Community-Sensor-Lab/Air-Quality-Sensor/Content/10. AQS-PCB-Mount.md

**Finding Files \-** File for both the PCB and Senserion Mount will be located on the [Community Sensor Github](https://github.com/Community-Sensor-Lab/Air-Quality-Sensor/tree/master) 

- Download and import the STL files into your 3D Printing Software  
- Add supports wherever required

****

---

**Mounting**

- When the two mounts are completed thread the holes with a 6-32 thread (Not required on newest mount iterations)  

- Secure the AQS Mount onto the top hole with a Grainger \#6 Screw (6-32 x 12'' Phillip Head Screw) with a 6-32 lock nut and a Phillips Bit or 6-32 x 12” Screw with a 6-32 lock nut and a H2.5 Bit. (Make sure that the PCB is screwed into the side with the Lip. So that the PCB will be secure in a vertical position)  
    
- Insert the Sen5X into the Mount  

- Make sure that the holes line up for the SEX5X Mount and the PCB Board  
    
- Secure the SEN5X Mount using the hole in the middle of the PCB. 6-32 x 12” Screw with a 6-32 lock nut and a H2.5 Bit or 6-32 x 12'' Phillip Head Screw (This mount should be on the back of the PCB with all the soldered joints)  

- Insert the AQS into a 3in PVC Pipe. (It is a tight fit so try to use moderate pressure. While rotating the AQS for it to be fully placed into the PVC Pipe.)

[image1]: <>

[image2]: <>

[image3]: <>
