Community-Sensor-Lab/Air-Quality-Sensor/Content/5. Code-Activity.md

Code Activity  
	In this section we're going to get an understanding on where the main code comes from by merging example codes. When merging example codes, we’ll be able to test and run two sensors at once. For this exercise we’ll be using the SparkFun single shot code and the BME280 test code.   
	If you don’t already have the library installed; be sure to install SparkFun SCD4x Arduino Library through the library manager. As this is where you will be able to find the single shot example code. 

Opening Up Both Example Codes  
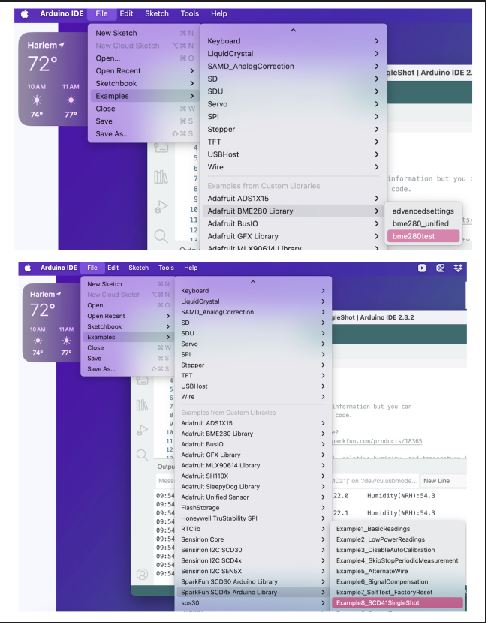
[picture p43: images/Code_Activity1.JPG]
  
SCD41SingleShot Edit  
	  
Before we continue we will have to make a slight modification to the code. Highlight lines 76 through 92 and click command forward slash (mac) or control forward slash (windows). This will comment out that section of the code, so that the section is disabled when uploading it. Also change line 35 to false,false,false. 

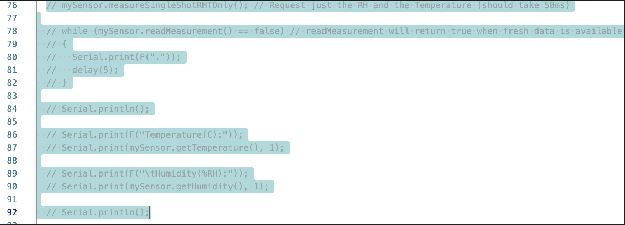
[picture p44: images/Code_Activity2.JPG]


Now we have everything read to start merging the code.

Procedure

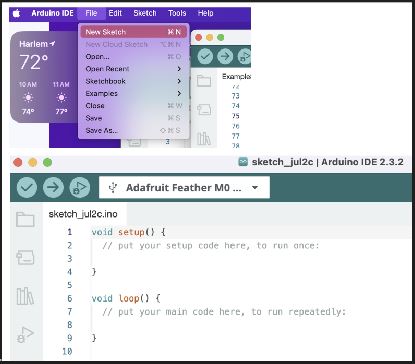
[picture p45: images/Code_Activity3.JPG]
1. Let’s start off by creating and setting up our new sketch.  
2. In the sketch we will start off by creating tabs for our functions  
   1. We will have four tabs:  
      1. SCD41\_initial   
      2. BME280\_initial  
      3. SCD41\_loop  
      4. BME280\_loop  
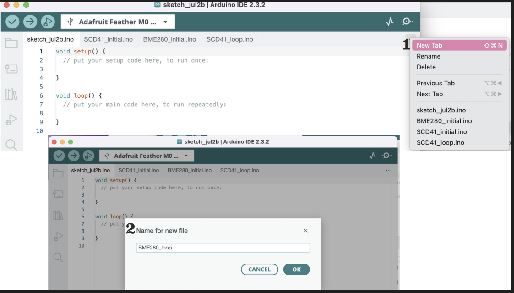
[picture p46: images/Code_Activity4.JPG]
   2. Creating these functions will help us better manage our code.  
3. Start by copying over the section before void setup() from both example codes and pasting it on to our new sketch before void setup().  

4. Next copy over the code for each tab we have created.  
     
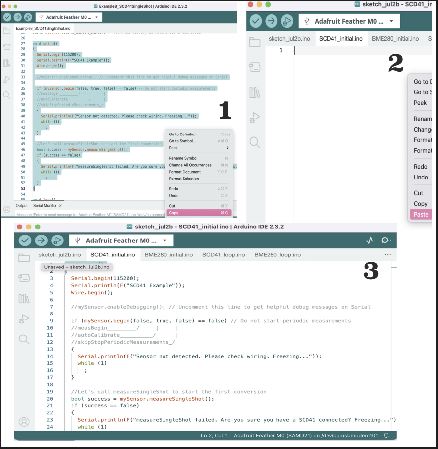
[picture p47: images/Code_Activity5.JPG]
   1. For the SCD 41\_initial we will copy over the void setup() code    
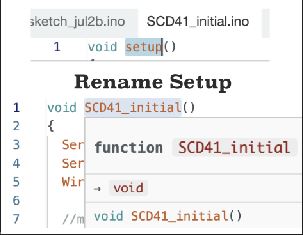
[picture p48: images/Code_Activity6.JPG]
      1. Next we will give the function a new name by replacing setup() with SCD41\_initial (recommended) or choose your own name.  
      2. Choose a good name as it will stick and you want to be able to easily identify the function  
   2. Repeat the same steps for the BME280\_initial tab.  
      1. Copy the void setup code  
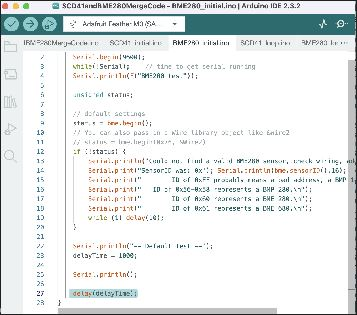
[picture p49: images/Code_Activity7.JPG]
      2. Paste it into the tab   
         1. Add “ delay(delayTime); ” into the end of the function as shown above   
      3. Remove printValues() in line 70 under void loop(););  
         1. Copy and Paste lines 76 to line 93 into Void loop. This function should be put under the tab BME280\_loop.  
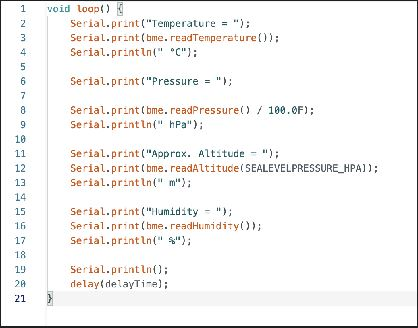
[picture p50: images/Code_Activity8.JPG]
            

      4. Rename the function  
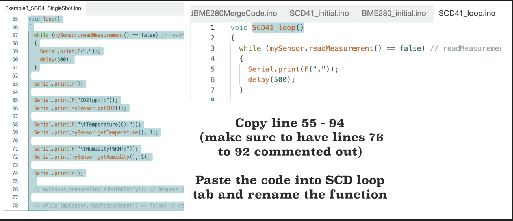
[picture p51: images/Code_Activity9.JPG]
   3. For the SCD 41 loop we will be copying the over the void loop code into the tab and renaming the function as well.  
   4. Repeat the same process for copying over the BME 280 loop into the BME280\_loop tab.  
      1. Copy over the void printValues  
      2. And add delay(delayTime); under the Serial.println();

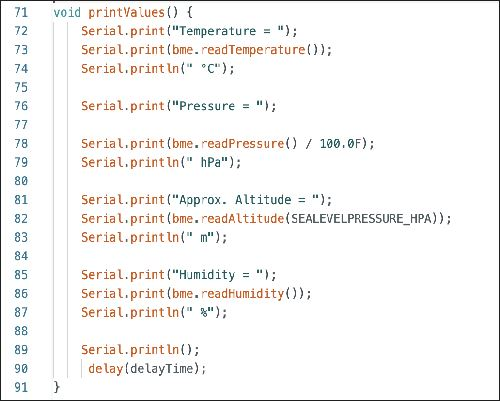
[picture p52: images/Code_Activity10.JPG]


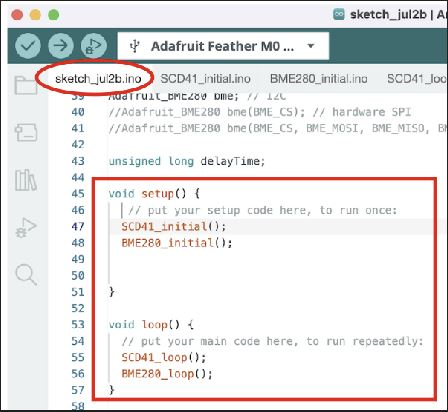
[picture p53: images/Code_Activity11.JPG]
5. Now we will add the functions we have created to the first tab like so;   
6. Our code is now complete\!  
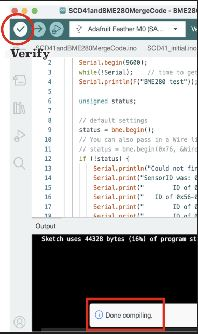
[picture p54: images/Code_Activity12.JPG]
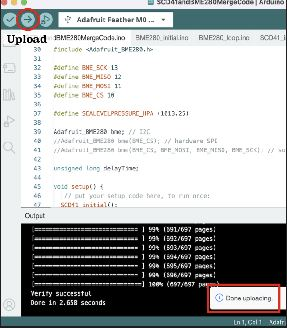
[picture p55: images/Code_Activity13.JPG]
7. Next step is to verify and upload the code to our sensors    
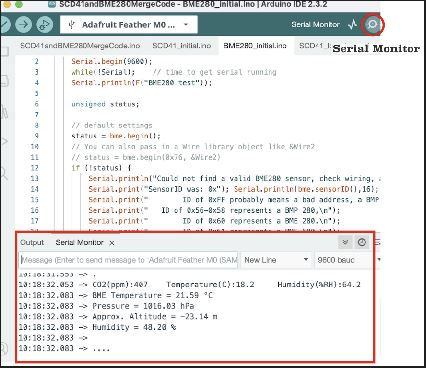
[picture p56: images/Code_Activity14.JPG]
8. Once the upload is complete press the serial monitor at the top right corner to see your data results.

[image1]: <>

[image2]: <>

[image3]: <>

[image4]: <>

[image5]: <>

[image6]: <>

[image7]: <>

[image8]: <>

[image9]: <>

[image10]: <>

[image11]: <>

[image12]: <>

[image13]: <>

[image14]: <>
