Community-Sensor-Lab/Air-Quality-Sensor/Content/image-1.png

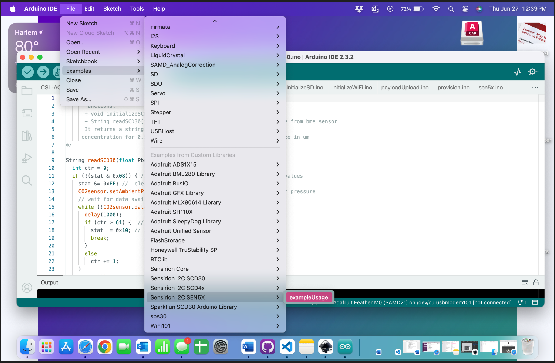
Content/image-1.png
