Community-Sensor-Lab/Air-Quality-Sensor/Content/image.png

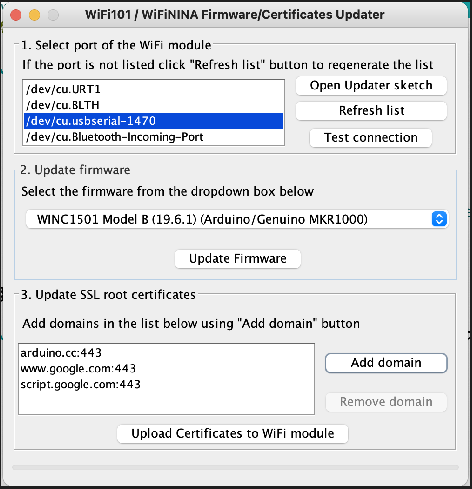
Content/image.png
