Community-Sensor-Lab/Air-Quality-Sensor/Contents/air_mon_system_sqr1.png

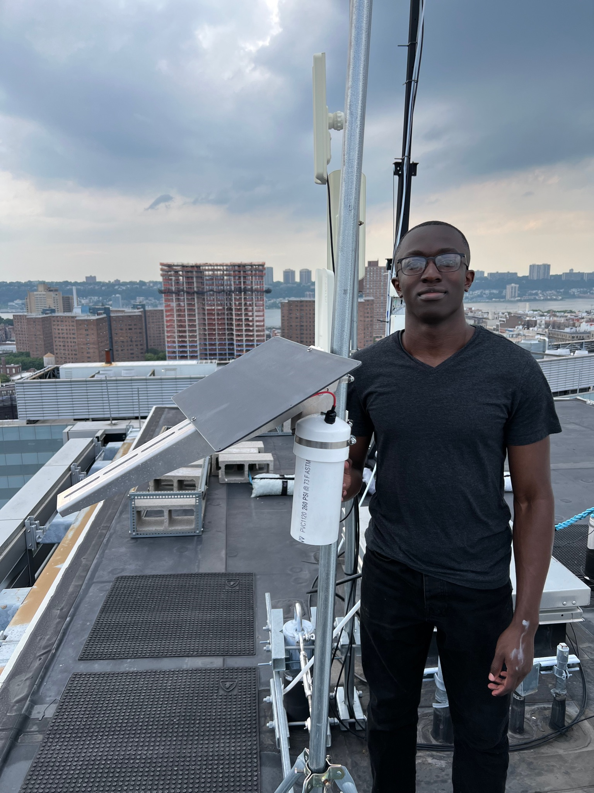
Contents/air_mon_system_sqr1.png
