Community-Sensor-Lab/Air-Quality-Sensor/Contents/CSL_AQS_solar_sqr.png

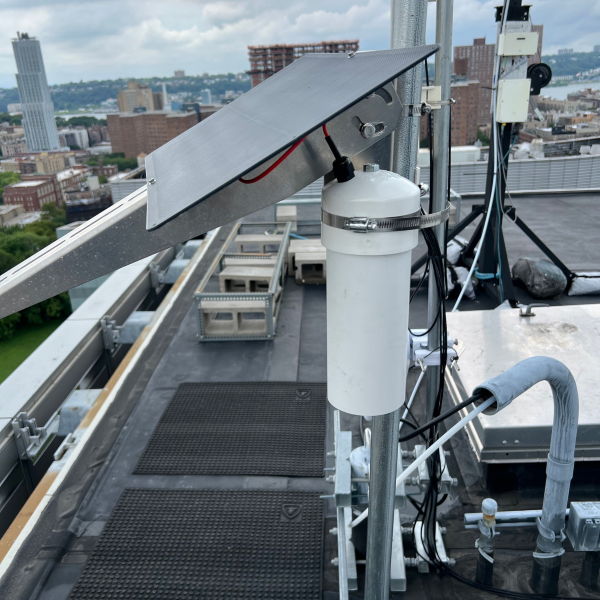
Contents/CSL_AQS_solar_sqr.png
