Community-Sensor-Lab/Air-Quality-Sensor/Contents/image-52.png

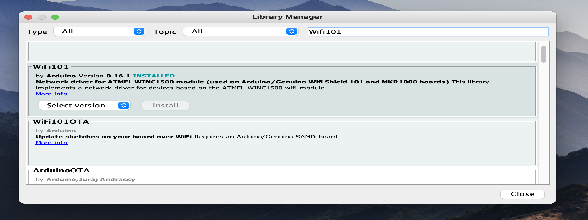
Contents/image-52.png
