Community-Sensor-Lab/Air-Quality-Sensor/Contents/image-53.png

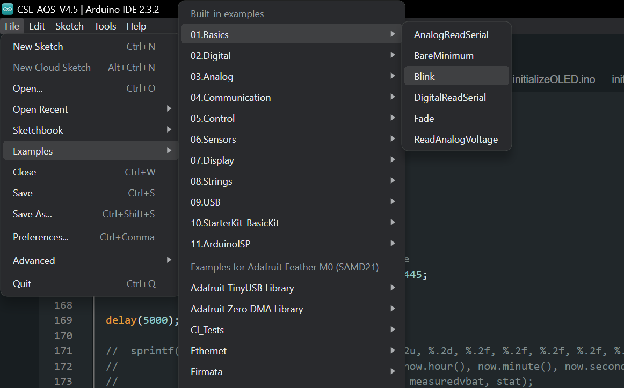
Contents/image-53.png
