Community-Sensor-Lab/Air-Quality-Sensor/Contents/image-54.png

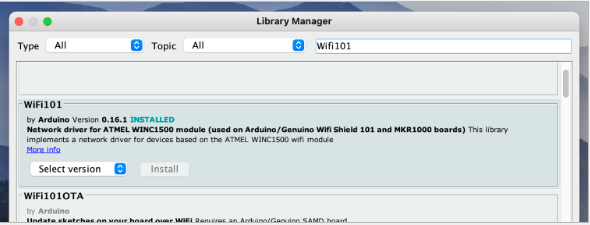
Contents/image-54.png
