Community-Sensor-Lab/Air-Quality-Sensor/Contents/image-55.png

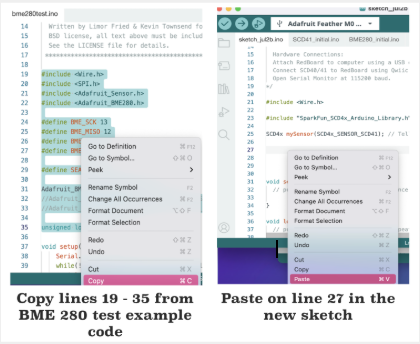
Contents/image-55.png
