Community-Sensor-Lab/Air-Quality-Sensor/Contents/resized_images/image-21.png

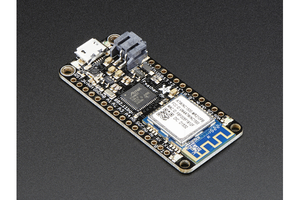
Contents/resized_images/image-21.png
