Community-Sensor-Lab/Air-Quality-Sensor/Contents/resized_images/image-22.png

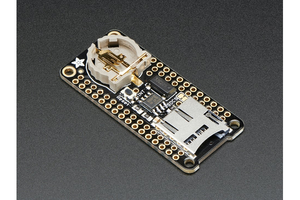
Contents/resized_images/image-22.png
