Community-Sensor-Lab/Air-Quality-Sensor/Contents/resized_images/image-23.png

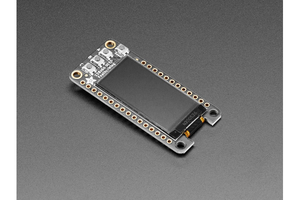
Contents/resized_images/image-23.png
