Community-Sensor-Lab/Air-Quality-Sensor/Contents/resized_images/image-24.png

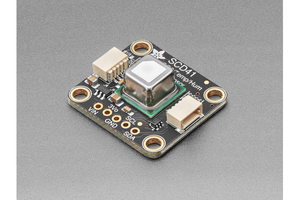
Contents/resized_images/image-24.png
