Community-Sensor-Lab/Air-Quality-Sensor/Contents/resized_images/image-25.png

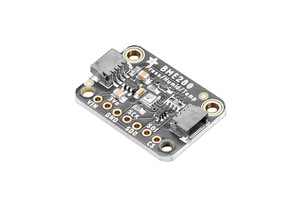
Contents/resized_images/image-25.png
