Community-Sensor-Lab/Air-Quality-Sensor/Contents/resized_images/image-26.png

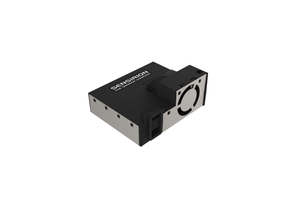
Contents/resized_images/image-26.png
