Community-Sensor-Lab/Air-Quality-Sensor/Contents/resized_images/image-27.png

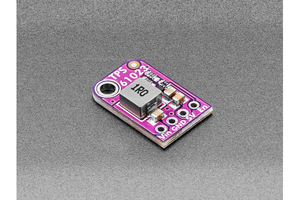
Contents/resized_images/image-27.png
