Community-Sensor-Lab/Air-Quality-Sensor/Contents/resized_images/image-28.png

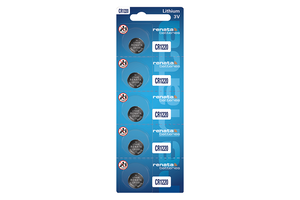
Contents/resized_images/image-28.png
