Community-Sensor-Lab/Air-Quality-Sensor/Contents/resized_images/image-29.png

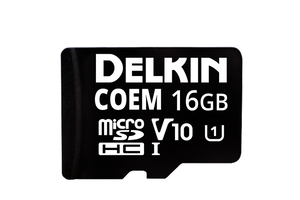
Contents/resized_images/image-29.png
