Community-Sensor-Lab/Air-Quality-Sensor/Contents/resized_images/image-30.png

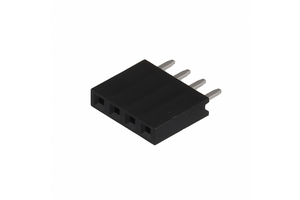
Contents/resized_images/image-30.png
