Community-Sensor-Lab/Air-Quality-Sensor/Contents/resized_images/image-31.png

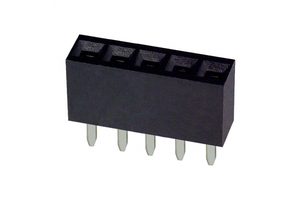
Contents/resized_images/image-31.png
