Community-Sensor-Lab/Air-Quality-Sensor/Contents/resized_images/image-32.png

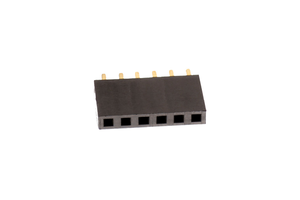
Contents/resized_images/image-32.png
