Community-Sensor-Lab/Air-Quality-Sensor/Contents/resized_images/image-33.png

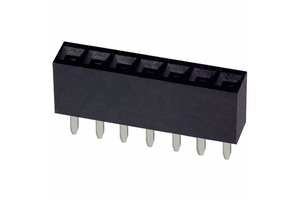
Contents/resized_images/image-33.png
