Community-Sensor-Lab/Air-Quality-Sensor/Contents/resized_images/image-34.png

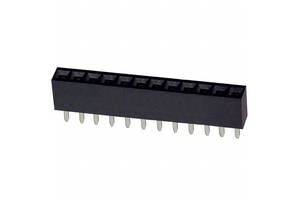
Contents/resized_images/image-34.png
