Community-Sensor-Lab/Air-Quality-Sensor/Contents/resized_images/image-36.png

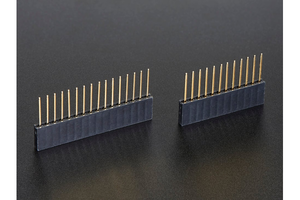
Contents/resized_images/image-36.png
