Community-Sensor-Lab/Air-Quality-Sensor/Contents/resized_images/image-37.png

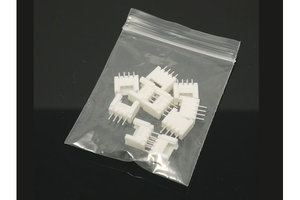
Contents/resized_images/image-37.png
