Community-Sensor-Lab/Air-Quality-Sensor/Contents/resized_images/image-38.png

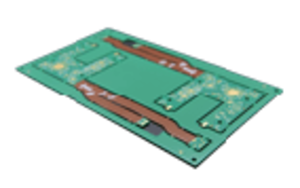
Contents/resized_images/image-38.png
