Community-Sensor-Lab/Air-Quality-Sensor/Contents/resized_images/image-39.png

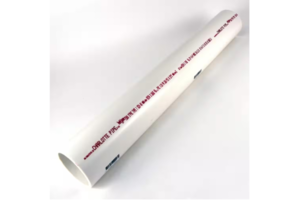
Contents/resized_images/image-39.png
