Community-Sensor-Lab/Air-Quality-Sensor/Contents/resized_images/image-40.png

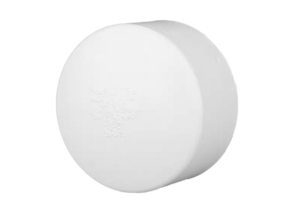
Contents/resized_images/image-40.png
