Community-Sensor-Lab/Air-Quality-Sensor/Contents/resized_images/image-41.png

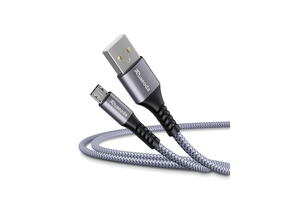
Contents/resized_images/image-41.png
