Community-Sensor-Lab/Air-Quality-Sensor/Contents/resized_images/image-42.png

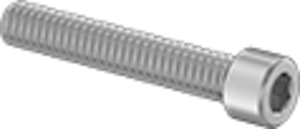
Contents/resized_images/image-42.png
