Community-Sensor-Lab/Air-Quality-Sensor/Contents/resized_images/image-43.png

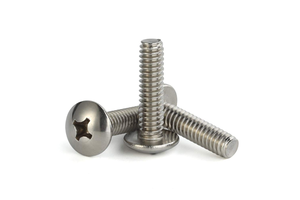
Contents/resized_images/image-43.png
