Community-Sensor-Lab/Air-Quality-Sensor/Contents/resized_images/image-44.png

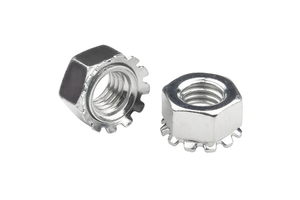
Contents/resized_images/image-44.png
