Community-Sensor-Lab/Air-Quality-Sensor/Contents/resized_images/image-45.png

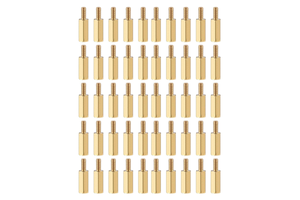
Contents/resized_images/image-45.png
