Community-Sensor-Lab/Air-Quality-Sensor/Contents/resized_images/image-46.png

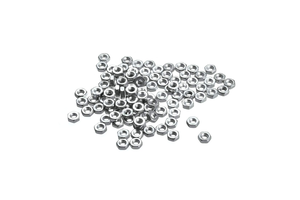
Contents/resized_images/image-46.png
