Community-Sensor-Lab/Air-Quality-Sensor/Contents/resized_images/image-47.png

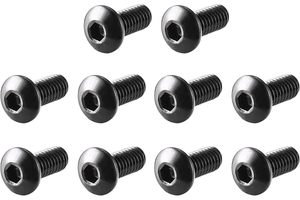
Contents/resized_images/image-47.png
