Community-Sensor-Lab/Air-Quality-Sensor/images/1954-02.jpg

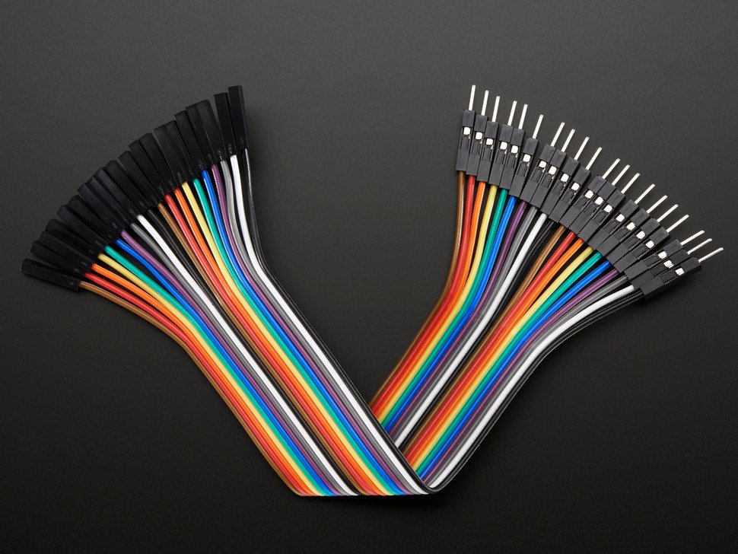
images/1954-02.jpg
