Community-Sensor-Lab/Air-Quality-Sensor/images/Adafruit BME280.png

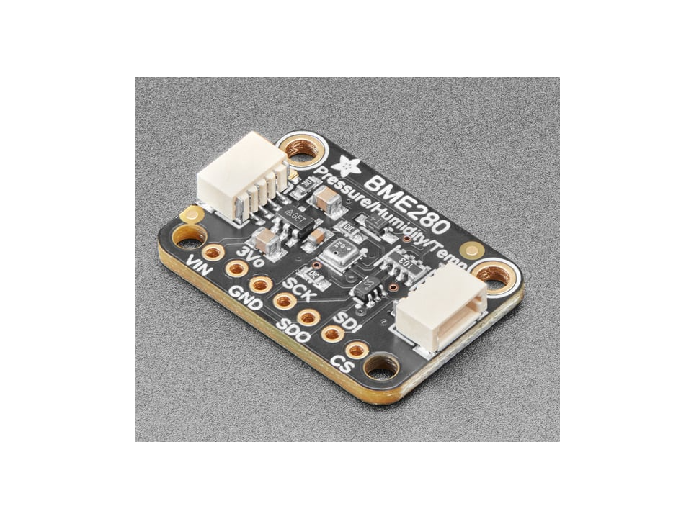
images/Adafruit BME280.png
