Community-Sensor-Lab/Air-Quality-Sensor/images/Adafruit_SCD-41.png

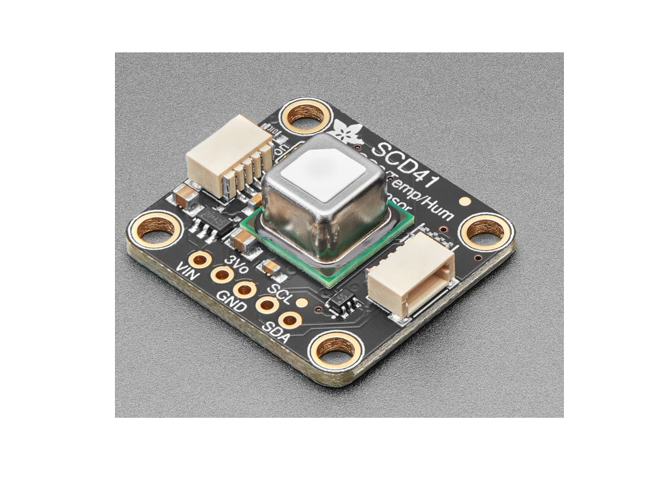
images/Adafruit_SCD-41.png
