Community-Sensor-Lab/Air-Quality-Sensor/images/Addalogger_FeatherWing.png

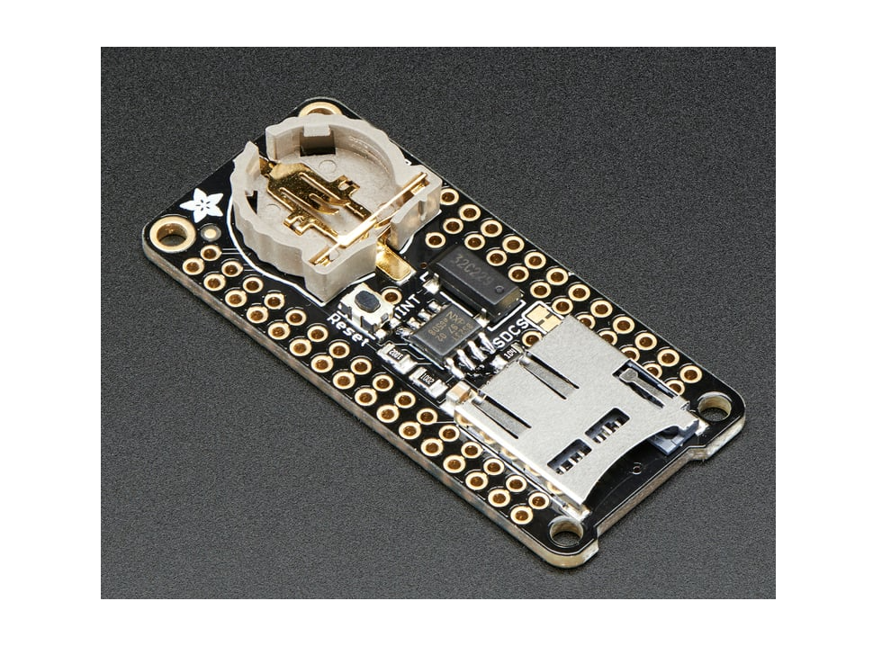
images/Addalogger_FeatherWing.png
