Community-Sensor-Lab/Air-Quality-Sensor/images/air-qaulity-sensor-V2.jpeg

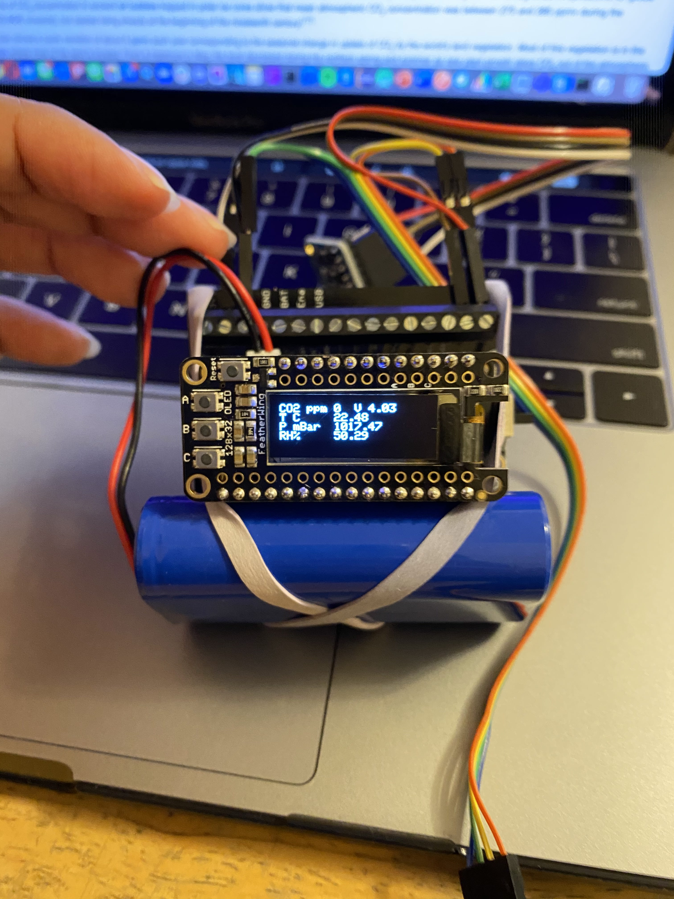
images/air-qaulity-sensor-V2.jpeg
