Community-Sensor-Lab/Air-Quality-Sensor/images/air_mon_system_sqr.png

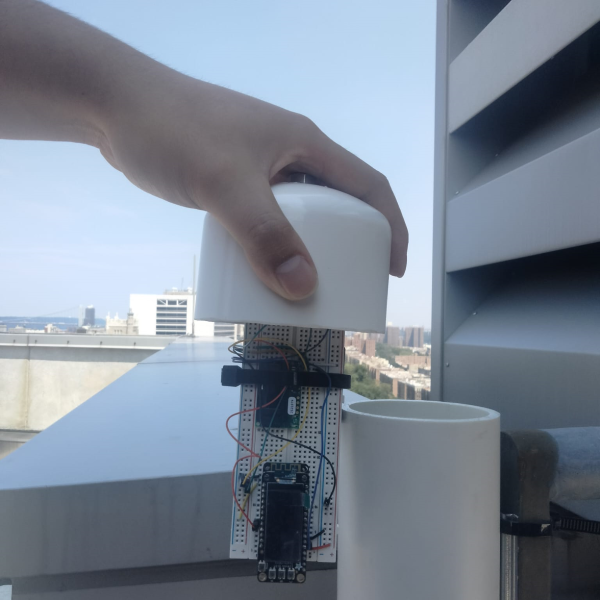
images/air_mon_system_sqr.png
