Community-Sensor-Lab/Air-Quality-Sensor/images/Battery-Coin-cr1220.jpeg

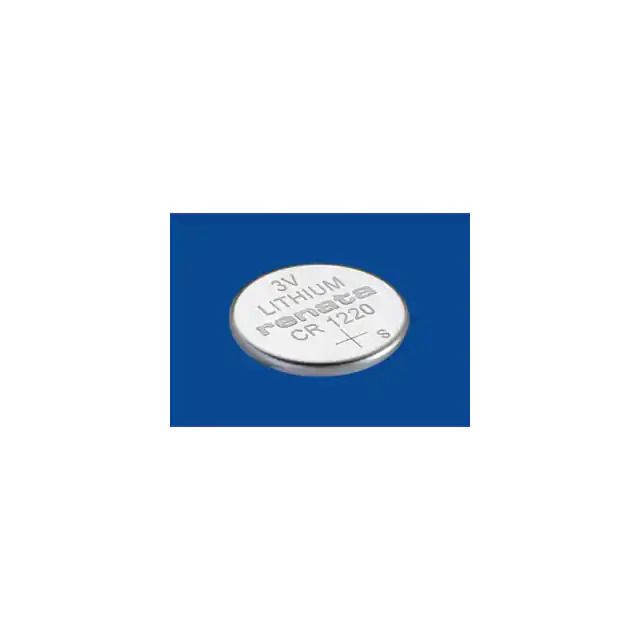
images/Battery-Coin-cr1220.jpeg
