Community-Sensor-Lab/Air-Quality-Sensor/images/Battery-Lithium-Polymer-LiPo-3.7V.jpeg

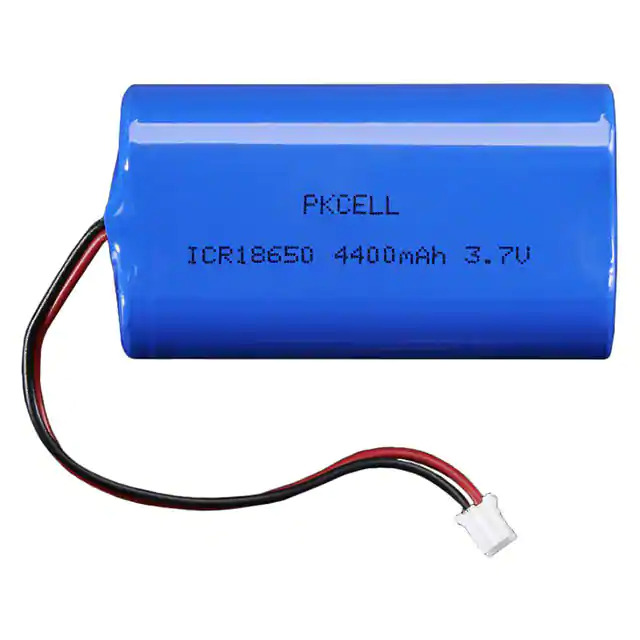
images/Battery-Lithium-Polymer-LiPo-3.7V.jpeg
