Community-Sensor-Lab/Air-Quality-Sensor/images/BME280.jpeg

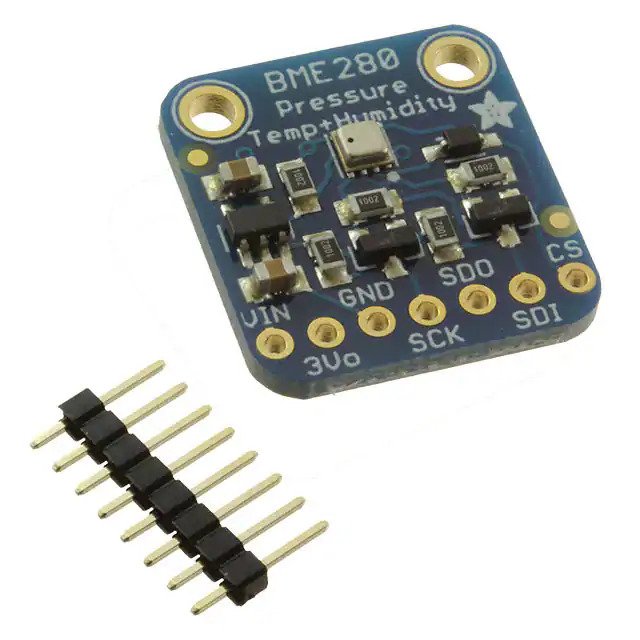
images/BME280.jpeg
