Community-Sensor-Lab/Air-Quality-Sensor/images/Charts_Spreadsheets1.JPG

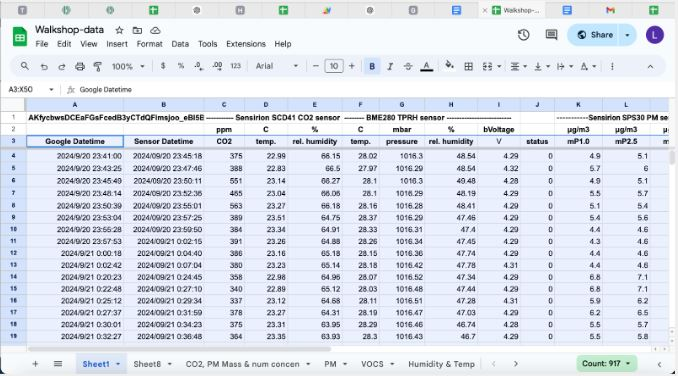
images/Charts_Spreadsheets1.JPG
