Community-Sensor-Lab/Air-Quality-Sensor/images/Charts_Spreadsheets2.JPG

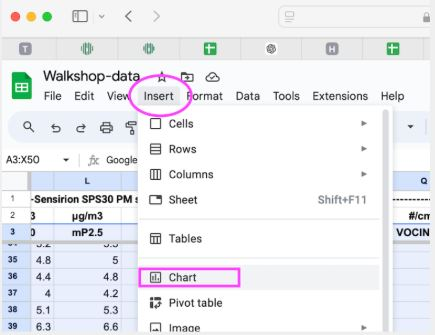
images/Charts_Spreadsheets2.JPG
