Community-Sensor-Lab/Air-Quality-Sensor/images/Charts_Spreadsheets3.JPG

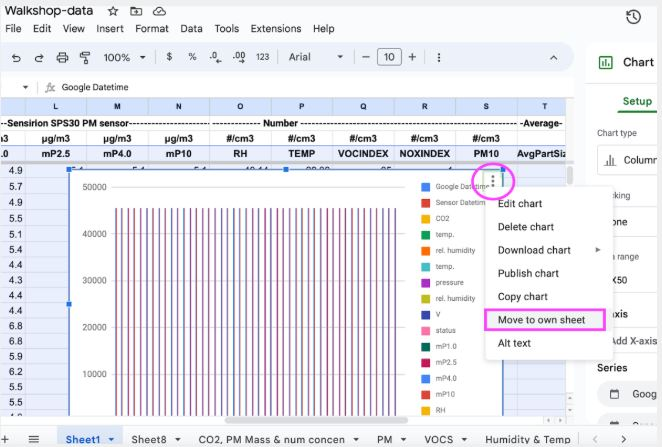
images/Charts_Spreadsheets3.JPG
