Community-Sensor-Lab/Air-Quality-Sensor/images/Charts_Spreadsheets4.JPG

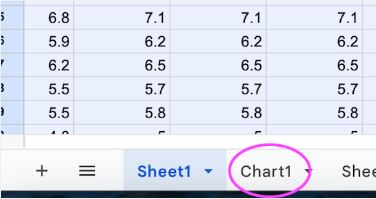
images/Charts_Spreadsheets4.JPG
