Community-Sensor-Lab/Air-Quality-Sensor/images/Charts_Spreadsheets5.JPG

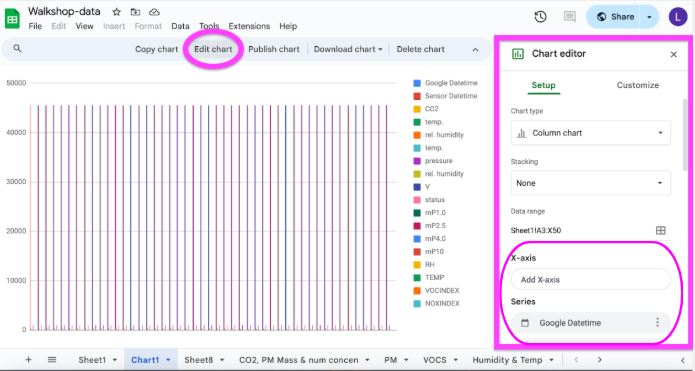
images/Charts_Spreadsheets5.JPG
