Community-Sensor-Lab/Air-Quality-Sensor/images/Charts_Spreadsheets6.JPG

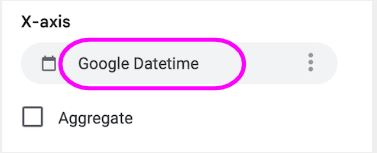
images/Charts_Spreadsheets6.JPG
