Community-Sensor-Lab/Air-Quality-Sensor/images/Charts_Spreadsheets7.JPG

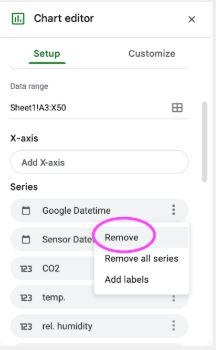
images/Charts_Spreadsheets7.JPG
