Community-Sensor-Lab/Air-Quality-Sensor/images/Charts_Spreadsheets8.JPG

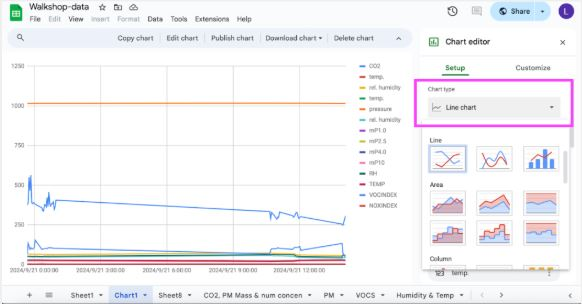
images/Charts_Spreadsheets8.JPG
