Community-Sensor-Lab/Air-Quality-Sensor/images/Charts_Spreadsheets9.JPG

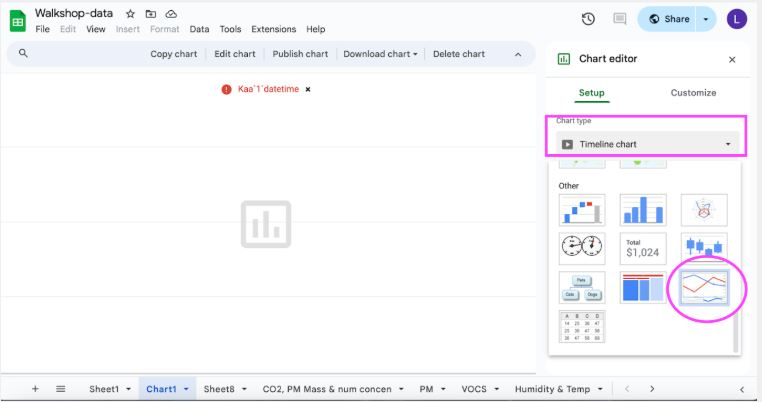
images/Charts_Spreadsheets9.JPG
