Community-Sensor-Lab/Air-Quality-Sensor/images/Charts_Spreadsheets10.JPG

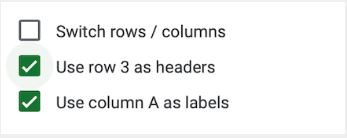
images/Charts_Spreadsheets10.JPG
