Community-Sensor-Lab/Air-Quality-Sensor/images/Charts_Spreadsheets12.JPG

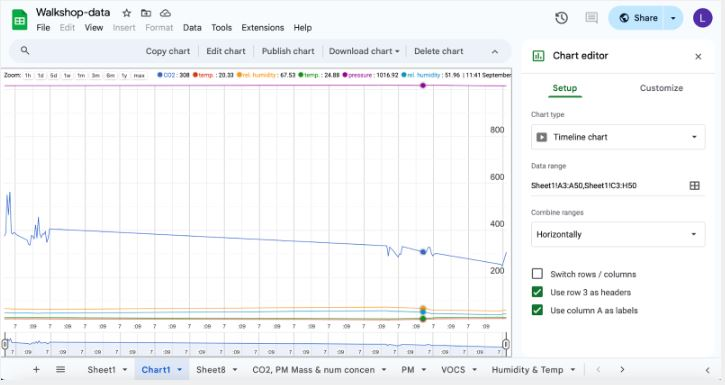
images/Charts_Spreadsheets12.JPG
