Community-Sensor-Lab/Air-Quality-Sensor/images/Charts_Spreadsheets13.JPG

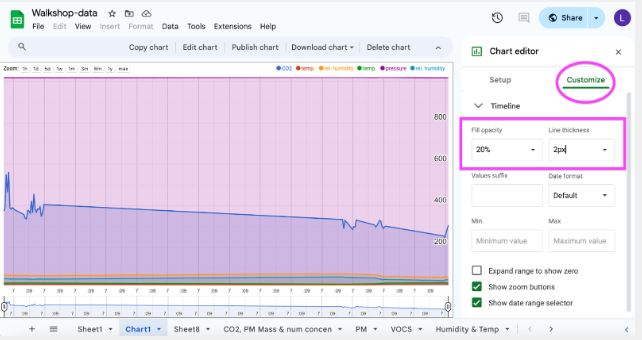
images/Charts_Spreadsheets13.JPG
