Community-Sensor-Lab/Air-Quality-Sensor/images/Code_Activity15.JPG

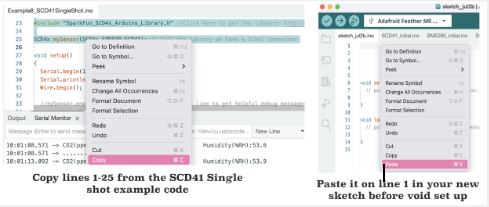
images/Code_Activity15.JPG
