Community-Sensor-Lab/Air-Quality-Sensor/images/CSL V3.0 diagram 1.png

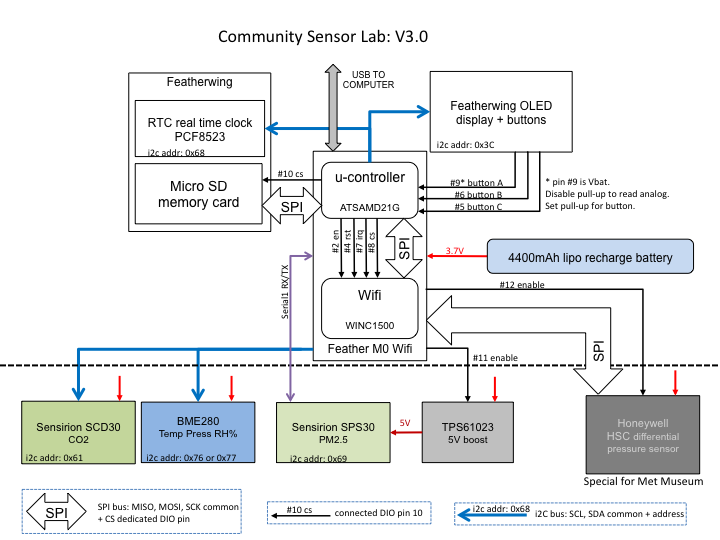
images/CSL V3.0 diagram 1.png
