Community-Sensor-Lab/Air-Quality-Sensor/images/CSL_AQS_solar2.jpg

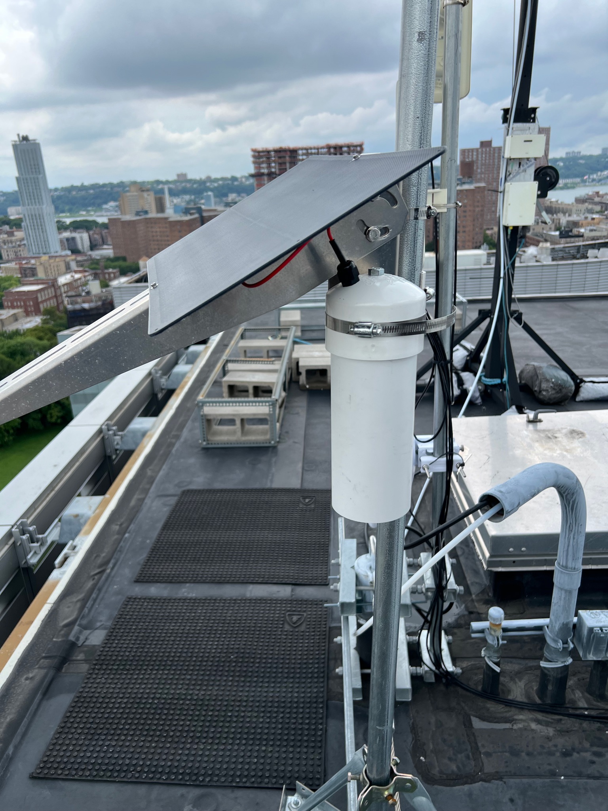
images/CSL_AQS_solar2.jpg
