Community-Sensor-Lab/Air-Quality-Sensor/images/Feather-M0-WiFi.jpeg

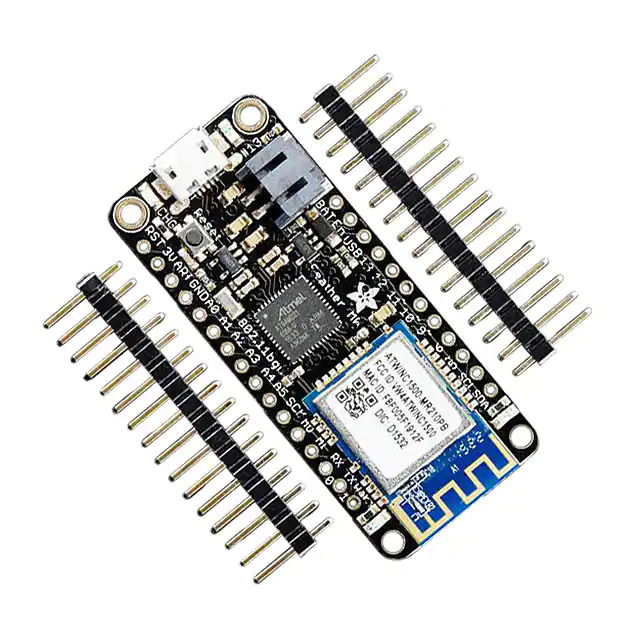
images/Feather-M0-WiFi.jpeg
