Community-Sensor-Lab/Air-Quality-Sensor/images/Feather-Terminal-Block.jpeg

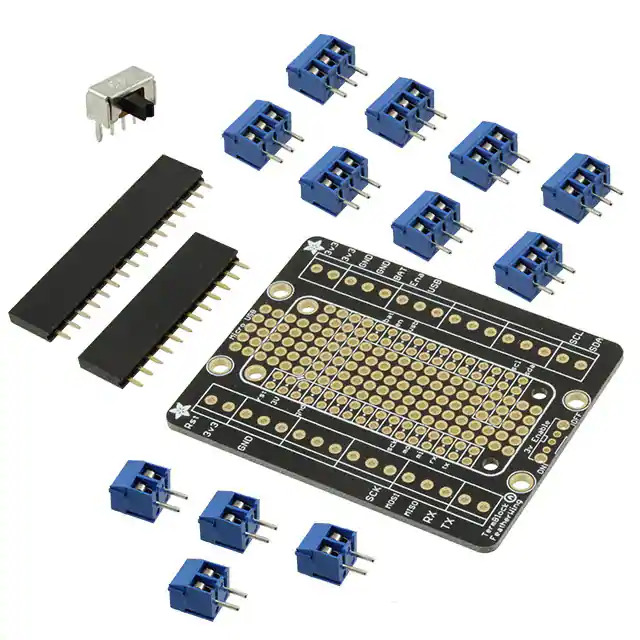
images/Feather-Terminal-Block.jpeg
