Community-Sensor-Lab/Air-Quality-Sensor/images/Feather_M0_Wifi.jpg

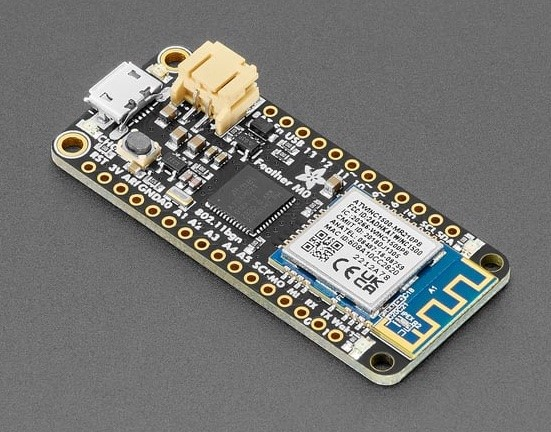
images/Feather_M0_Wifi.jpg
