Community-Sensor-Lab/Air-Quality-Sensor/images/Featherwing-Logger.jpeg

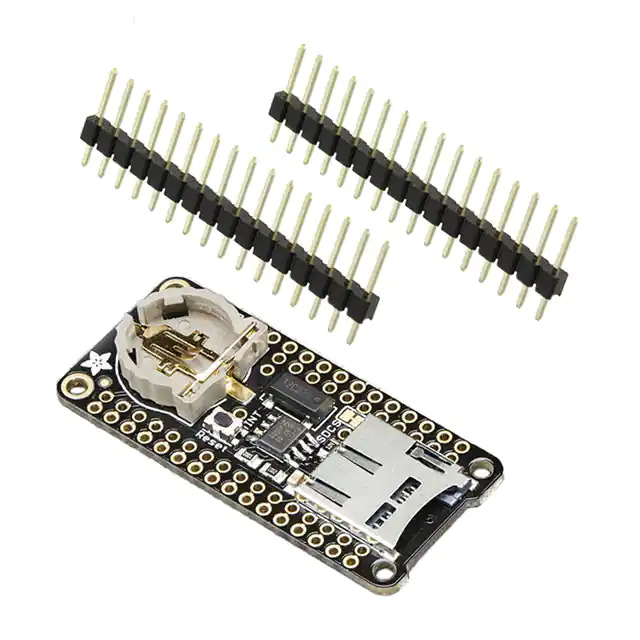
images/Featherwing-Logger.jpeg
