Community-Sensor-Lab/Air-Quality-Sensor/images/FeatherWing_OLED.png

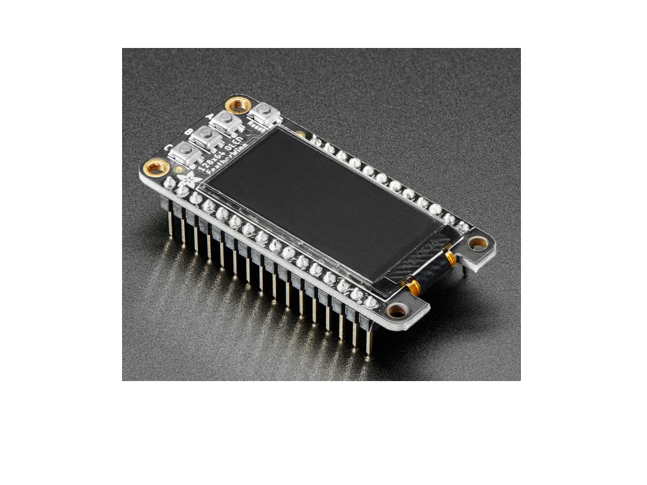
images/FeatherWing_OLED.png
