Community-Sensor-Lab/Air-Quality-Sensor/images/hero_spr.png

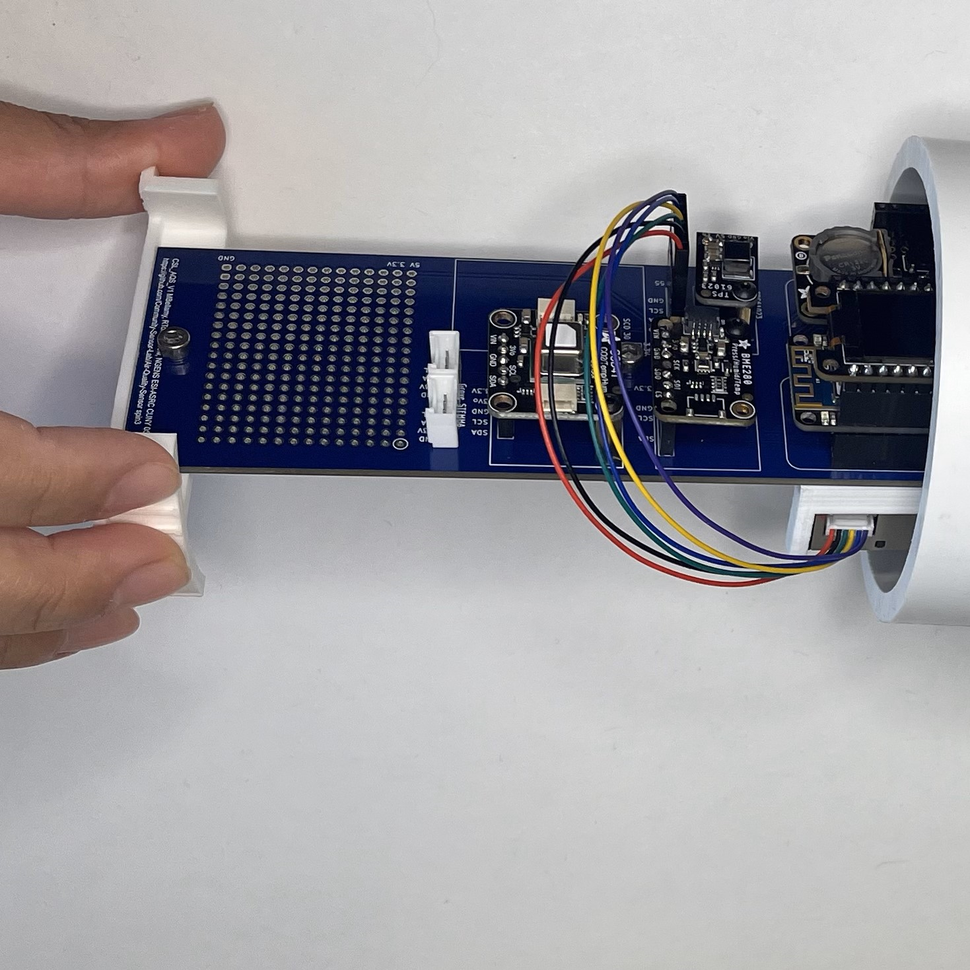
images/hero_spr.png
