Community-Sensor-Lab/Air-Quality-Sensor/images/hero_sqr3.png

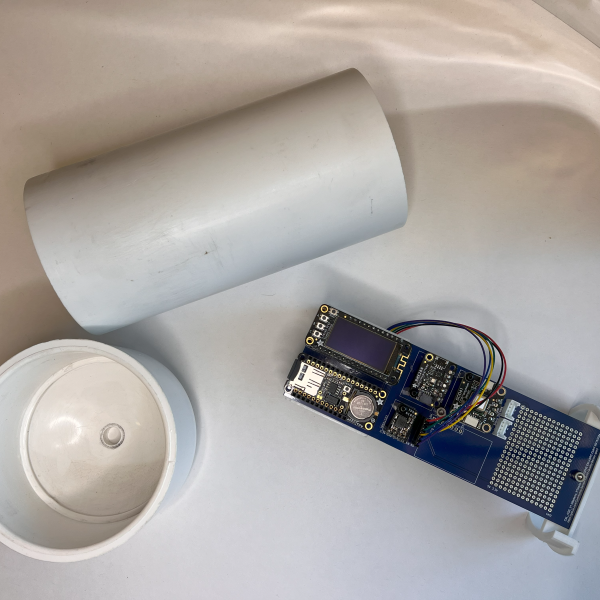
images/hero_sqr3.png
