Community-Sensor-Lab/Air-Quality-Sensor/images/hsc-differential-pressure.jpeg

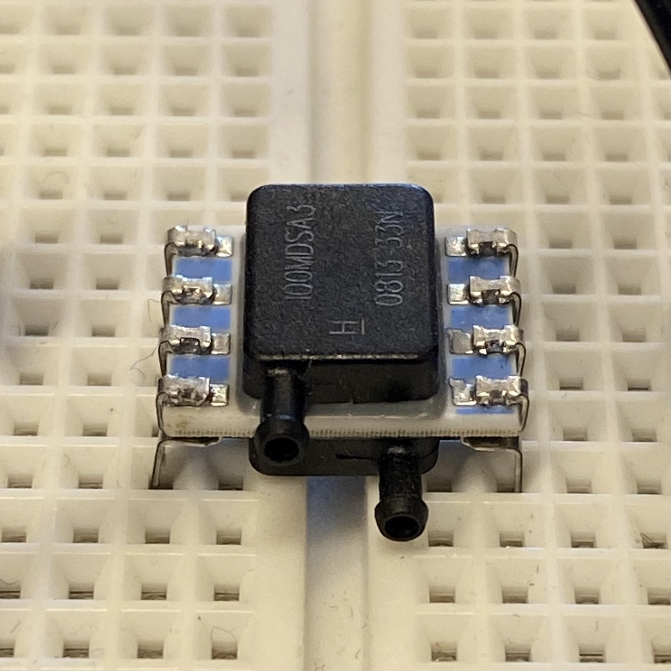
images/hsc-differential-pressure.jpeg
