Community-Sensor-Lab/Air-Quality-Sensor/images/IMG_2107.jpg

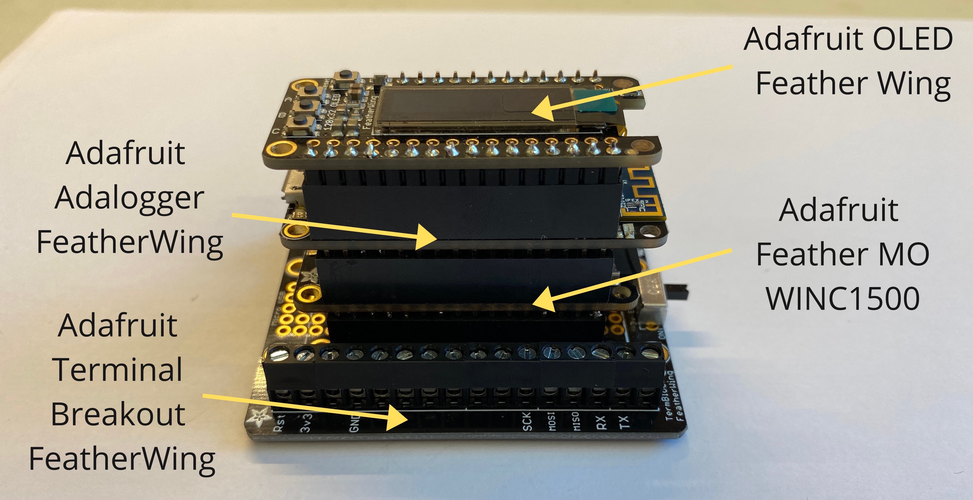
images/IMG_2107.jpg
