Community-Sensor-Lab/Air-Quality-Sensor/images/IMG_2110.JPG

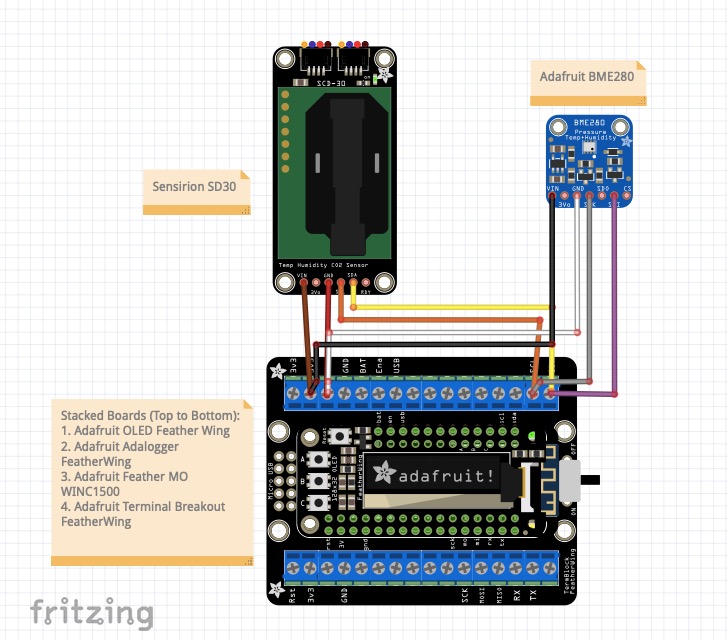
images/IMG_2110.JPG
