Community-Sensor-Lab/Air-Quality-Sensor/images/Micro-SD.jpeg

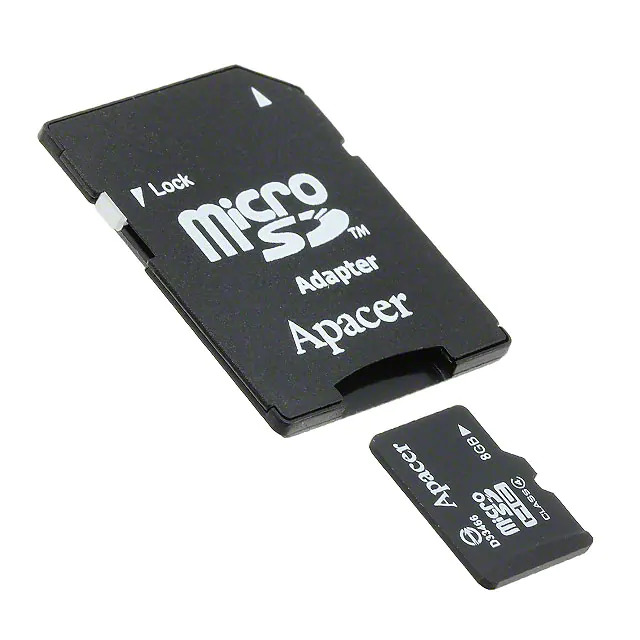
images/Micro-SD.jpeg
