Community-Sensor-Lab/Air-Quality-Sensor/images/miniboost-5v.jpeg

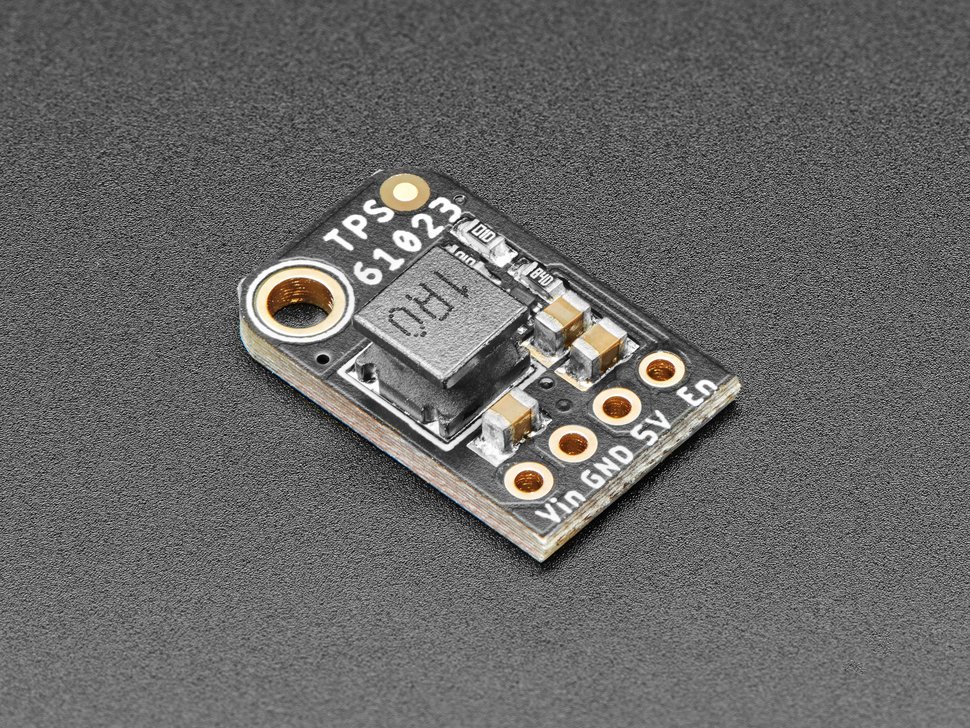
images/miniboost-5v.jpeg
