Community-Sensor-Lab/Air-Quality-Sensor/images/OLED.jpg

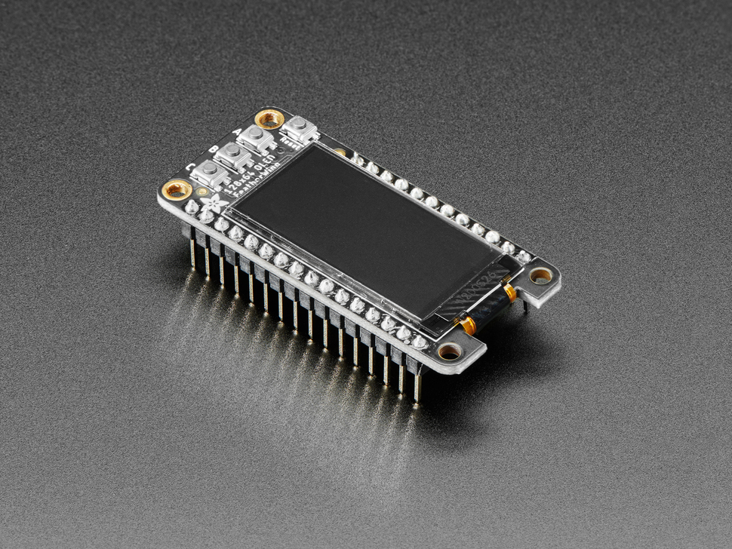
images/OLED.jpg
