Community-Sensor-Lab/Air-Quality-Sensor/images/SEN55_PM-AQS.png

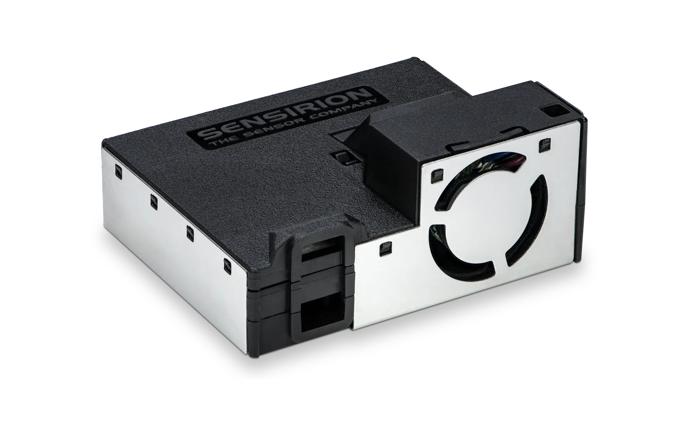
images/SEN55_PM-AQS.png
