Community-Sensor-Lab/Air-Quality-Sensor/images/Sensirion-SPS380-PM25.jpg

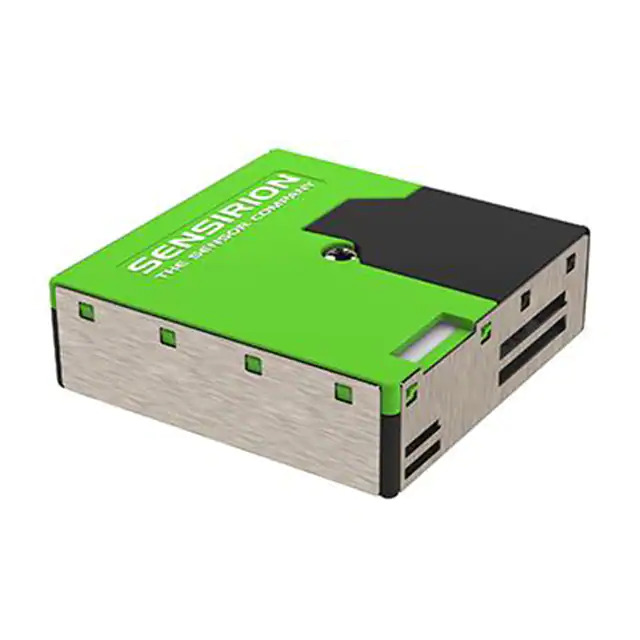
images/Sensirion-SPS380-PM25.jpg
