Community-Sensor-Lab/Air-Quality-Sensor/images/Sensirion_SD30_CO2_NDIR.jpeg

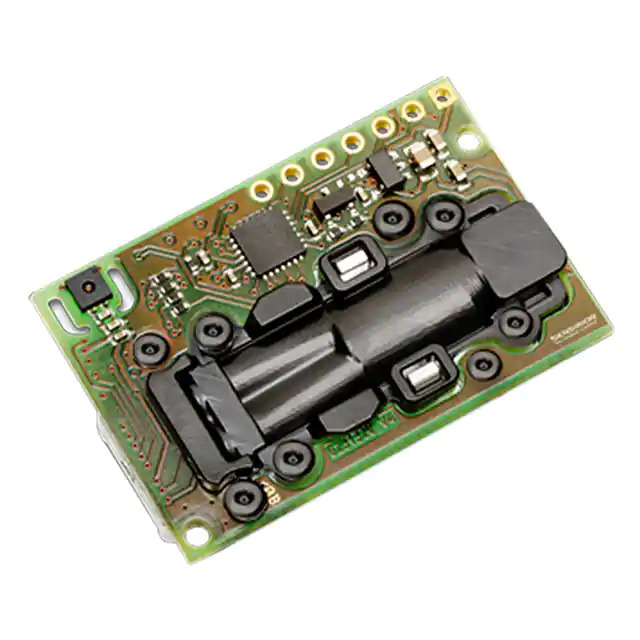
images/Sensirion_SD30_CO2_NDIR.jpeg
