Community-Sensor-Lab/Air-Quality-Sensor/images/WIFI LOGGER CSL-AQS-V2.0.png

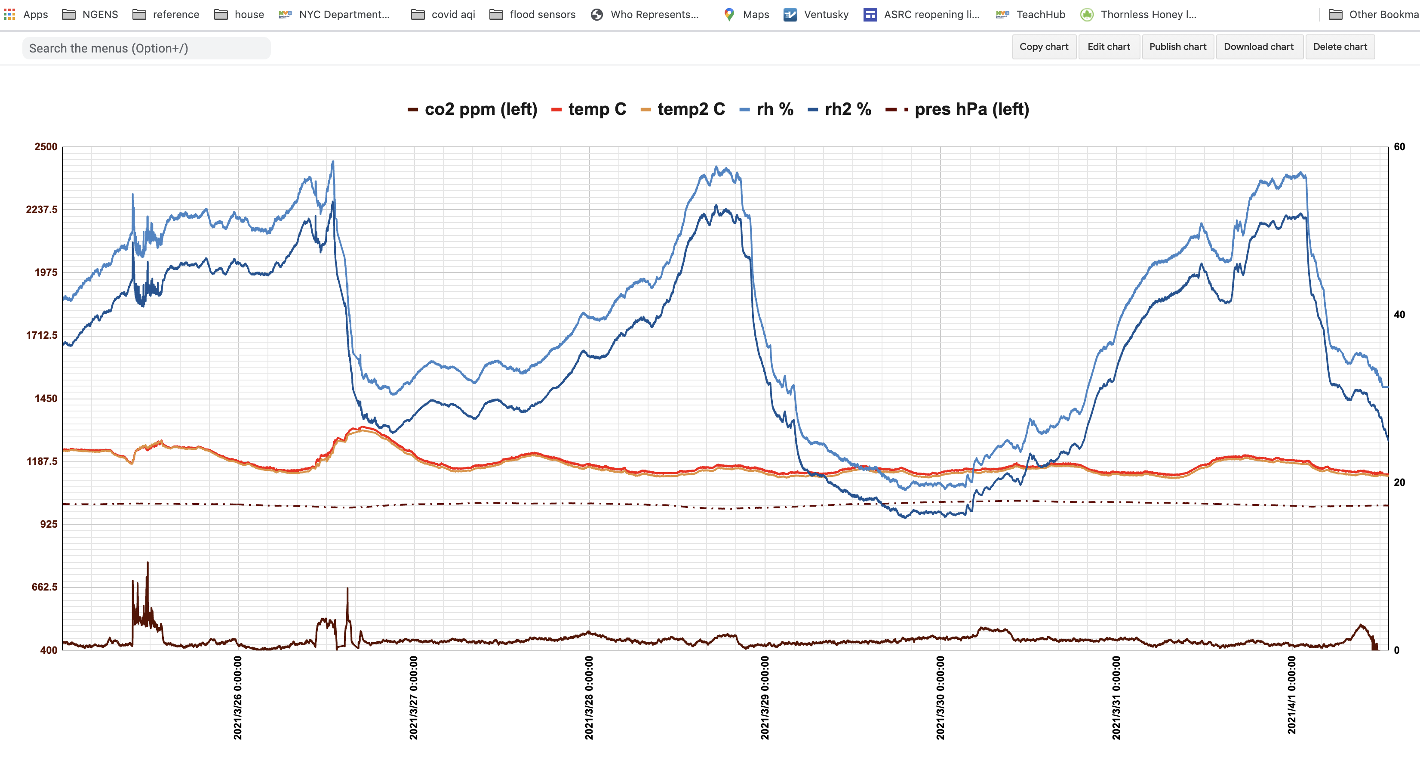
images/WIFI LOGGER CSL-AQS-V2.0.png
