Community-Sensor-Lab/Air-Quality-Sensor/images/Design-and-Assembly-of-PCB1.png

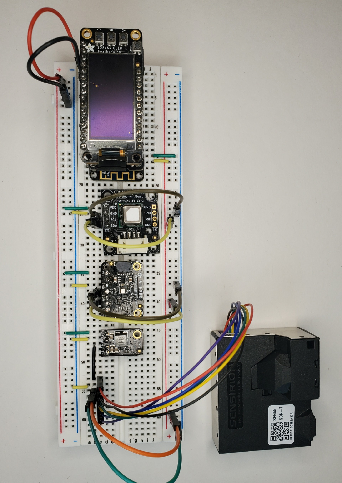
images/Design-and-Assembly-of-PCB1.png
