Community-Sensor-Lab/Air-Quality-Sensor/images/Design-and-Assembly-of-PCB2.png

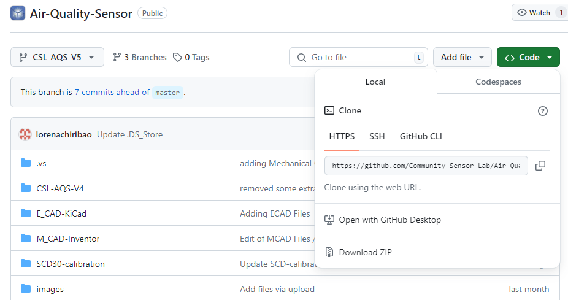
images/Design-and-Assembly-of-PCB2.png
