Community-Sensor-Lab/Air-Quality-Sensor/images/Design-and-Assembly-of-PCB3.png

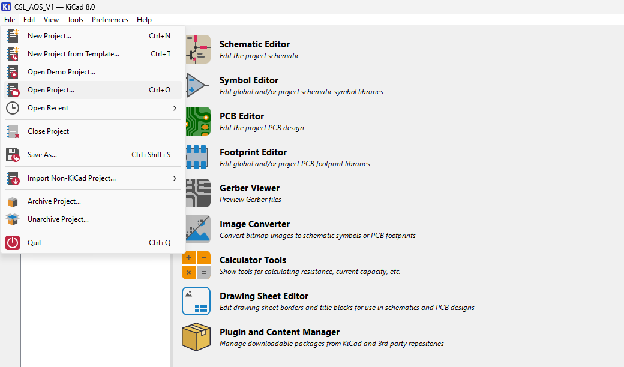
images/Design-and-Assembly-of-PCB3.png
