Community-Sensor-Lab/Air-Quality-Sensor/images/Design-and-Assembly-of-PCB4.png

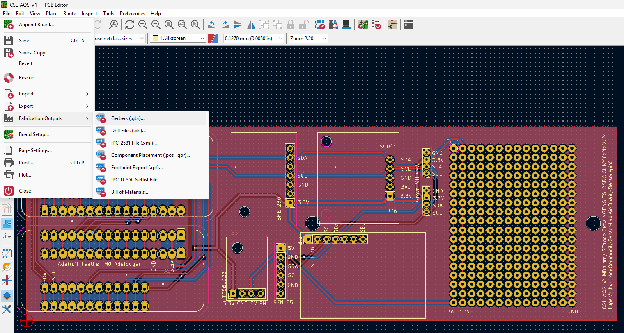
images/Design-and-Assembly-of-PCB4.png
