Community-Sensor-Lab/Air-Quality-Sensor/images/Design-and-Assembly-of-PCB5.png

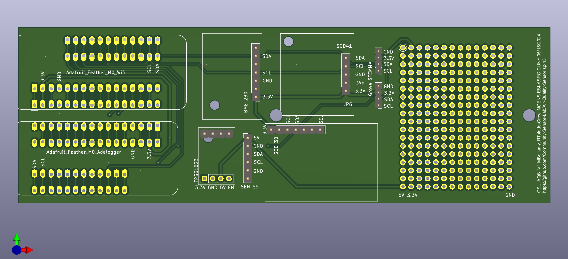
images/Design-and-Assembly-of-PCB5.png
