Community-Sensor-Lab/Air-Quality-Sensor/images/Design-and-Assembly-of-PCB6.png

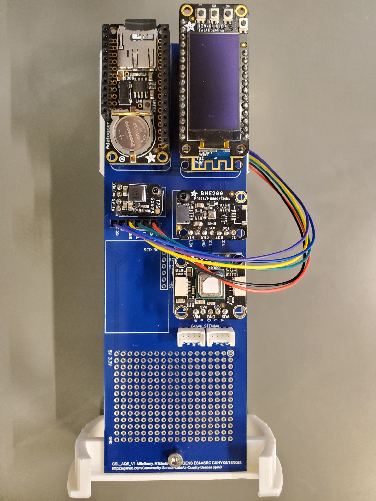
images/Design-and-Assembly-of-PCB6.png
