Community-Sensor-Lab/Air-Quality-Sensor/images/Installing_Arduino_236_Getting_Started6.JPG

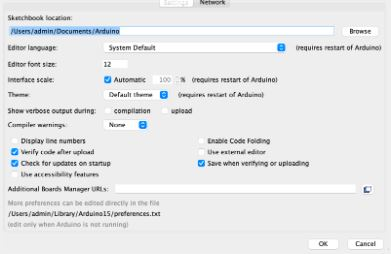
images/Installing_Arduino_236_Getting_Started6.JPG
